dev-campusfab/chessLab/Hardware/kiCad_chessLab/cell.kicad_sch

## KiCad design Hardware/kiCad_chessLab/cell.kicad_sch (2026-09-14)

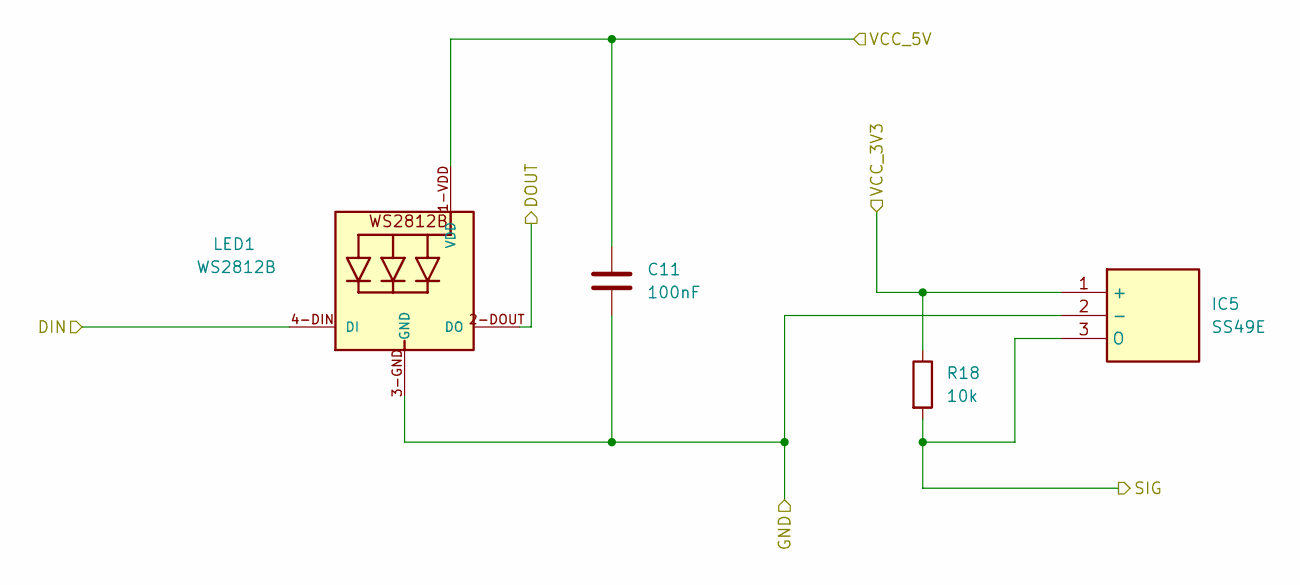
[picture p15: schematic cell.kicad_sch]

Parts:
C11: 100nF; C_0603_1608Metric_Pad1.08x0.95mm_HandSolder
IC5: SS49E; TO130P160X410X300-3P; Mouser Part Number 785-SS49E
LED1: WS2812B
R18: 10k; R_0603_1608Metric_Pad0.98x0.95mm_HandSolder

Connections:
DIN: LED1.4-DIN (DI)
DOUT: LED1.2-DOUT (DO)
GND: C11.2, IC5.2 (-), LED1.3-GND (GND)
SIG: IC5.3 (O), R18.2
VCC_3V3: IC5.1 (+), R18.1
VCC_5V: C11.1, LED1.1-VDD (VDD)
