dev-campusfab/chessLab/Hardware/kiCad_chessLab/main_board.kicad_sch

## KiCad design Hardware/kiCad_chessLab/main_board.kicad_sch (2026-09-17)

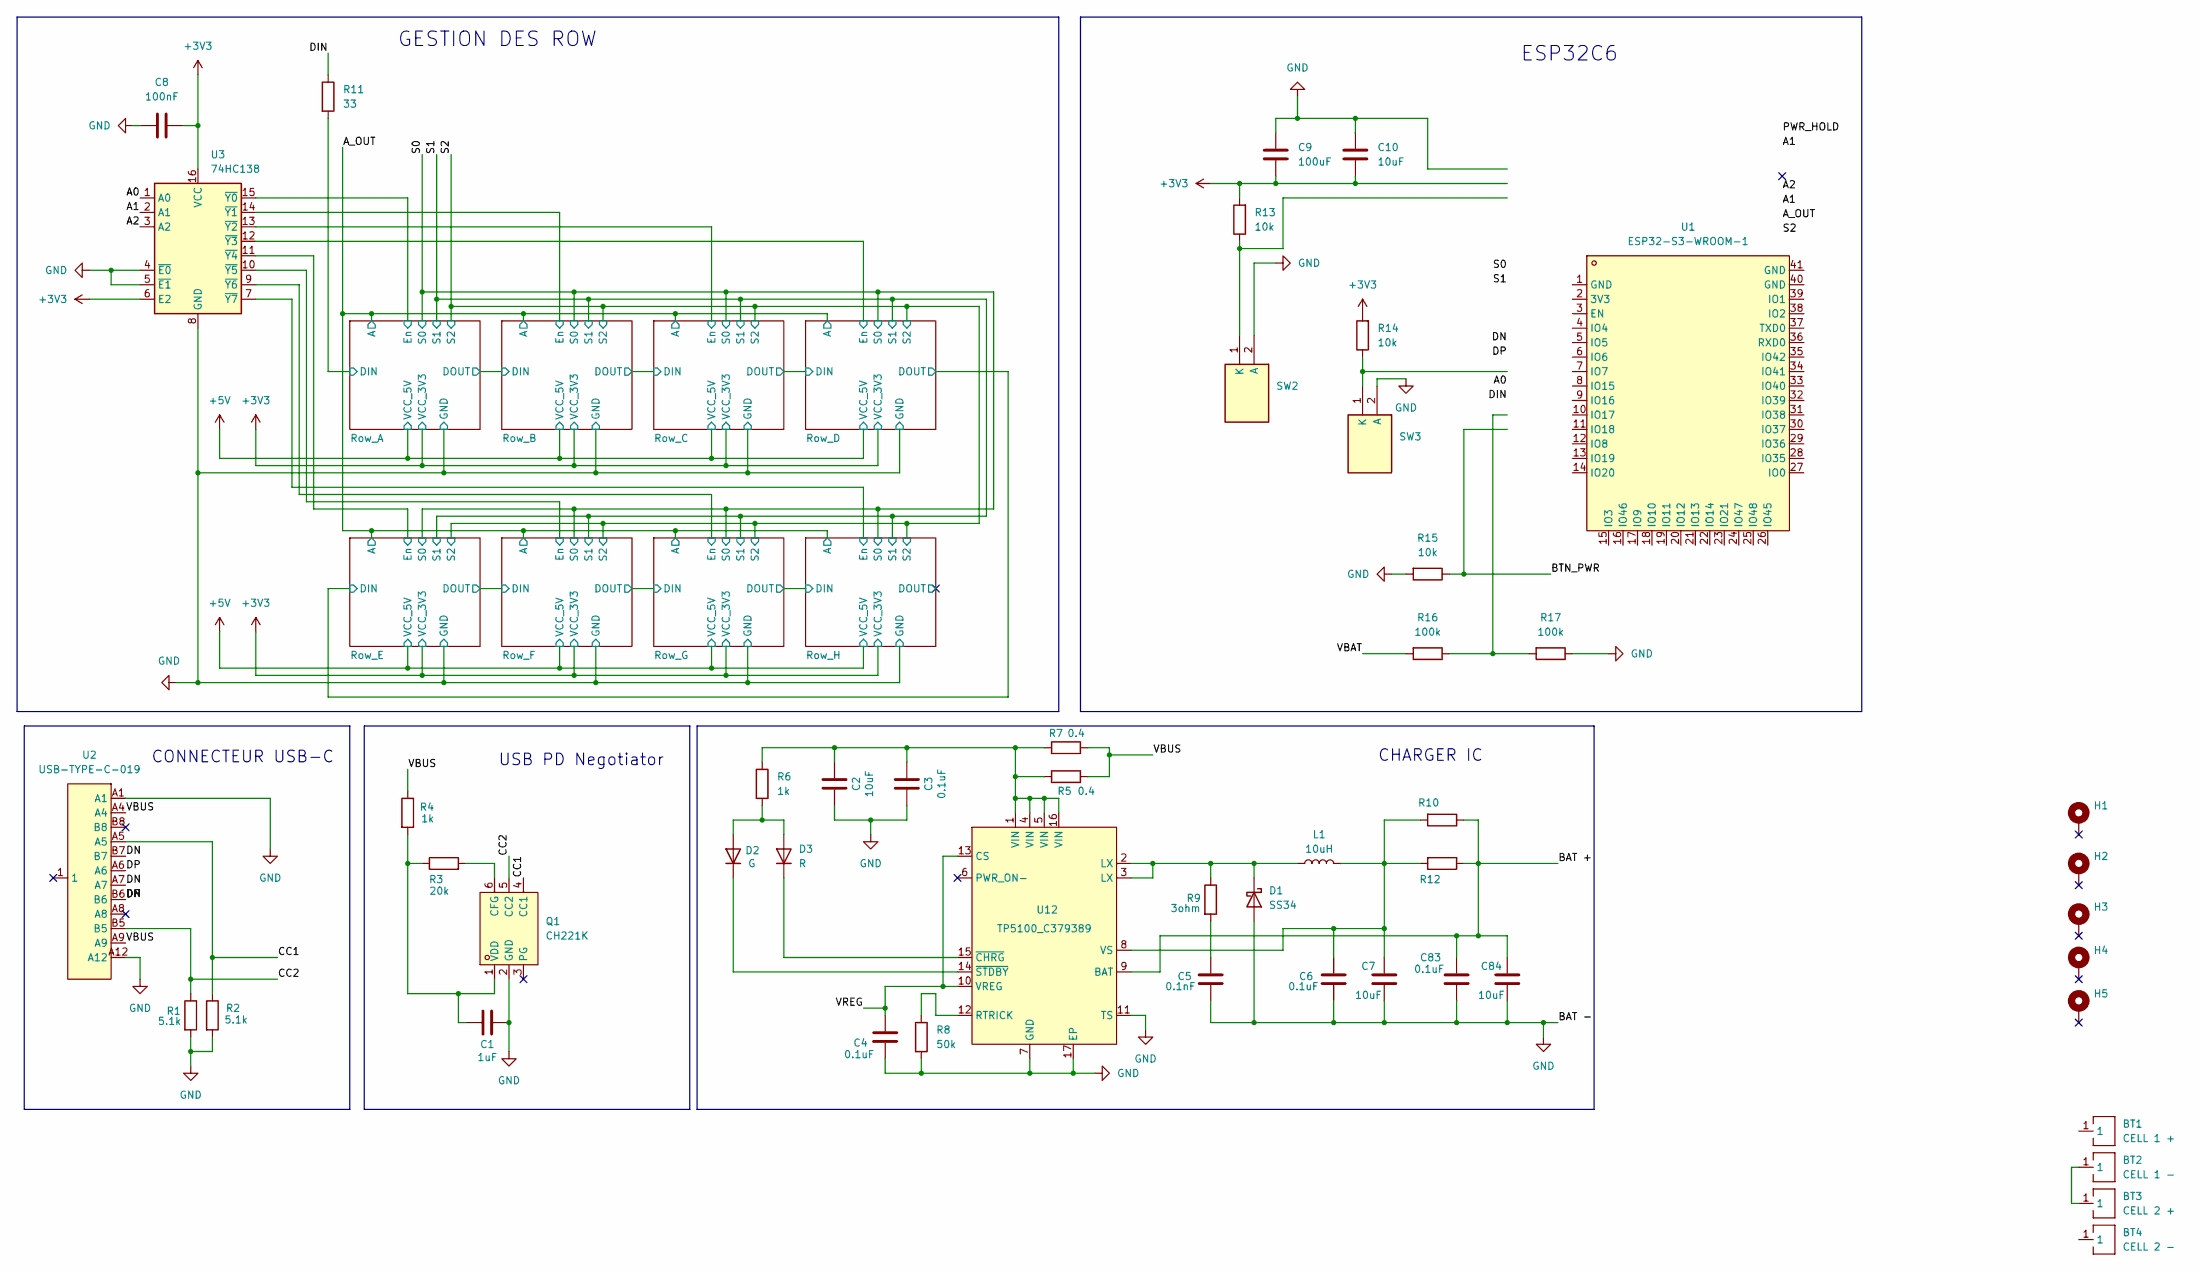
[picture p16: schematic main_board.kicad_sch]

Parts:
BT1: CELL 1 +; BAT-TH_MY-18650-01; MPN MY-18650-01; LCSC Part C2979183
BT2: CELL 1 -; BAT-TH_MY-18650-01; MPN MY-18650-01; LCSC Part C2979183
BT3: CELL 2 +; BAT-TH_MY-18650-01; MPN MY-18650-01; LCSC Part C2979183
BT4: CELL 2 -; BAT-TH_MY-18650-01; MPN MY-18650-01; LCSC Part C2979183
C1: 1uF; C_0201_0603Metric_Pad0.64x0.40mm_HandSolder
C2, C7, C84: 10uF; C_1210_3225Metric_Pad1.33x2.70mm_HandSolder
C3, C4, C6, C83: 0.1uF; C_0603_1608Metric_Pad1.08x0.95mm_HandSolder
C5: 0.1nF; C_0603_1608Metric_Pad1.08x0.95mm_HandSolder
C8: 100nF; C_0603_1608Metric_Pad1.08x0.95mm_HandSolder
C9: 100uF; C_0603_1608Metric_Pad1.08x0.95mm_HandSolder
C10: 10uF; C_0603_1608Metric_Pad1.08x0.95mm_HandSolder
D1: SS34; D_SMA_Handsoldering
D2: G; D_1206_3216Metric
D3: R; D_1206_3216Metric
H1, H2, H3, H4, H5: MountingHole_Pad; MountingHole_2.2mm_M2_DIN965_Pad
L1: 10uH; L_TechFuse_SL0520
Q1: CH221K; SOT-23-6_L2.9-W1.6-P0.95-LS2.8-BL-2; MPN CH221K; LCSC Part C5125736
R1, R2: 5.1k; R_0603_1608Metric_Pad0.98x0.95mm_HandSolder
R3: 20k; R_0603_1608Metric_Pad0.98x0.95mm_HandSolder
R4, R6: 1k; R_0603_1608Metric_Pad0.98x0.95mm_HandSolder
R5, R7: 0.4; R_1206_3216Metric_Pad1.30x1.75mm_HandSolder
R8: 50k; R_0603_1608Metric_Pad0.98x0.95mm_HandSolder
R9: 3ohm; R_0603_1608Metric_Pad0.98x0.95mm_HandSolder
R10, R12: 0,1; R_1206_3216Metric_Pad1.30x1.75mm_HandSolder
R11: 33; R_0603_1608Metric_Pad0.98x0.95mm_HandSolder
R13, R14, R15: 10k; R_0603_1608Metric_Pad0.98x0.95mm_HandSolder
R16, R17: 100k; R_0603_1608Metric_Pad0.98x0.95mm_HandSolder
SW2: RST; B3U-1000P; Mouser Part Number 653-B3U-1000P
SW3: BOOT; B3U-1000P; Mouser Part Number 653-B3U-1000P
U1: ESP32-S3-WROOM-1; WIRELM-SMD_ESP32-S3-WROOM-1; MPN ESP32-S3-WROOM-1-N16R2; LCSC Part C2913205
U2: USB-TYPE-C-019; TYPE-C-SMD_HX-TYPE-C-16PIN; MPN USB-TYPE-C-019; LCSC Part C2927039
U3: 74HC138; SOIC-16_3.9x9.9mm_P1.27mm
U12: TP5100_C379389; TQFN-16_L4.0-W4.0-P0.65-BL-EP; MPN TP5100; LCSC Part C379389

Connections:
+3V3: C8.2, C9.2, C10.2, R13.2, R14.2, U3.6 (E2), U3.16 (VCC)
A0: U3.1 (A0)
A1: U3.2 (A1)
A2: U3.3 (A2)
BAT +: C83.2, C84.2, R10.1, R12.1, U12.9 (BAT)
BTN_PWR: R15.1
CC1: Q1.4 (CC1), R2.1, U2.A5
CC2: Q1.5 (CC2), R1.1, U2.B5
DIN: R11.1, R11.2
DN: U2.A6, U2.A7, U2.B6, U2.B7
En: U3.7 (~Y7), U3.9 (~Y6), U3.10 (~Y5), U3.11 (~Y4), U3.12 (~Y3), U3.13 (~Y2), U3.14 (~Y1), U3.15 (~Y0)
GND: C1.2, C2.1, C3.1, C4.1, C5.1, C6.1, C7.1, C8.1, C9.1, C10.1, C83.1, C84.1, D1.2 (A), Q1.2 (GND), R1.2, R2.2, R8.2, R15.2, R17.1, SW2.2 (A), SW3.2 (A), U2.A1, U2.A12, U3.4 (~E0), U3.5 (~E1), U3.8 (GND), U12.7 (GND), U12.11 (TS), U12.17 (EP)
unnamed: BT2.1, BT3.1
unnamed: C1.1, Q1.1 (VDD), R3.1, R4.2
unnamed: C2.2, C3.2, R5.1, R6.1, R7.1, U12.1 (VIN), U12.4 (VIN), U12.5 (VIN), U12.16 (VIN)
unnamed: C5.2, R9.2
unnamed: C6.2, C7.2, L1.2, R10.2, R12.2, U12.8 (VS)
unnamed: D1.1 (K), L1.1, R9.1, U12.2 (LX), U12.3 (LX)
unnamed: D2.1 (K), U12.14 (~STDBY)
unnamed: D2.2 (A), D3.2 (A), R6.2
unnamed: D3.1 (K), U12.15 (~CHRG)
unnamed: Q1.6 (CFG), R3.2
unnamed: R8.1, U12.12 (RTRICK)
unnamed: R13.1, SW2.1 (K)
unnamed: R14.1, SW3.1 (K)
unnamed: R16.1, R17.2
VBAT: R16.2
VBUS: R4.1, R5.2, R7.2, U2.A4, U2.A9
VREG: C4.2, U12.10 (VREG), U12.13 (CS)

Notes on the sheet:
GESTION DES ROW
CHARGER IC
USB PD Negotiator
ESP32C6
CONNECTEUR USB-C
