dev-campusfab/chessLab/Hardware/kiCad_chessLab/power_board.kicad_sch

## KiCad design Hardware/kiCad_chessLab/power_board.kicad_sch (2026-09-14)

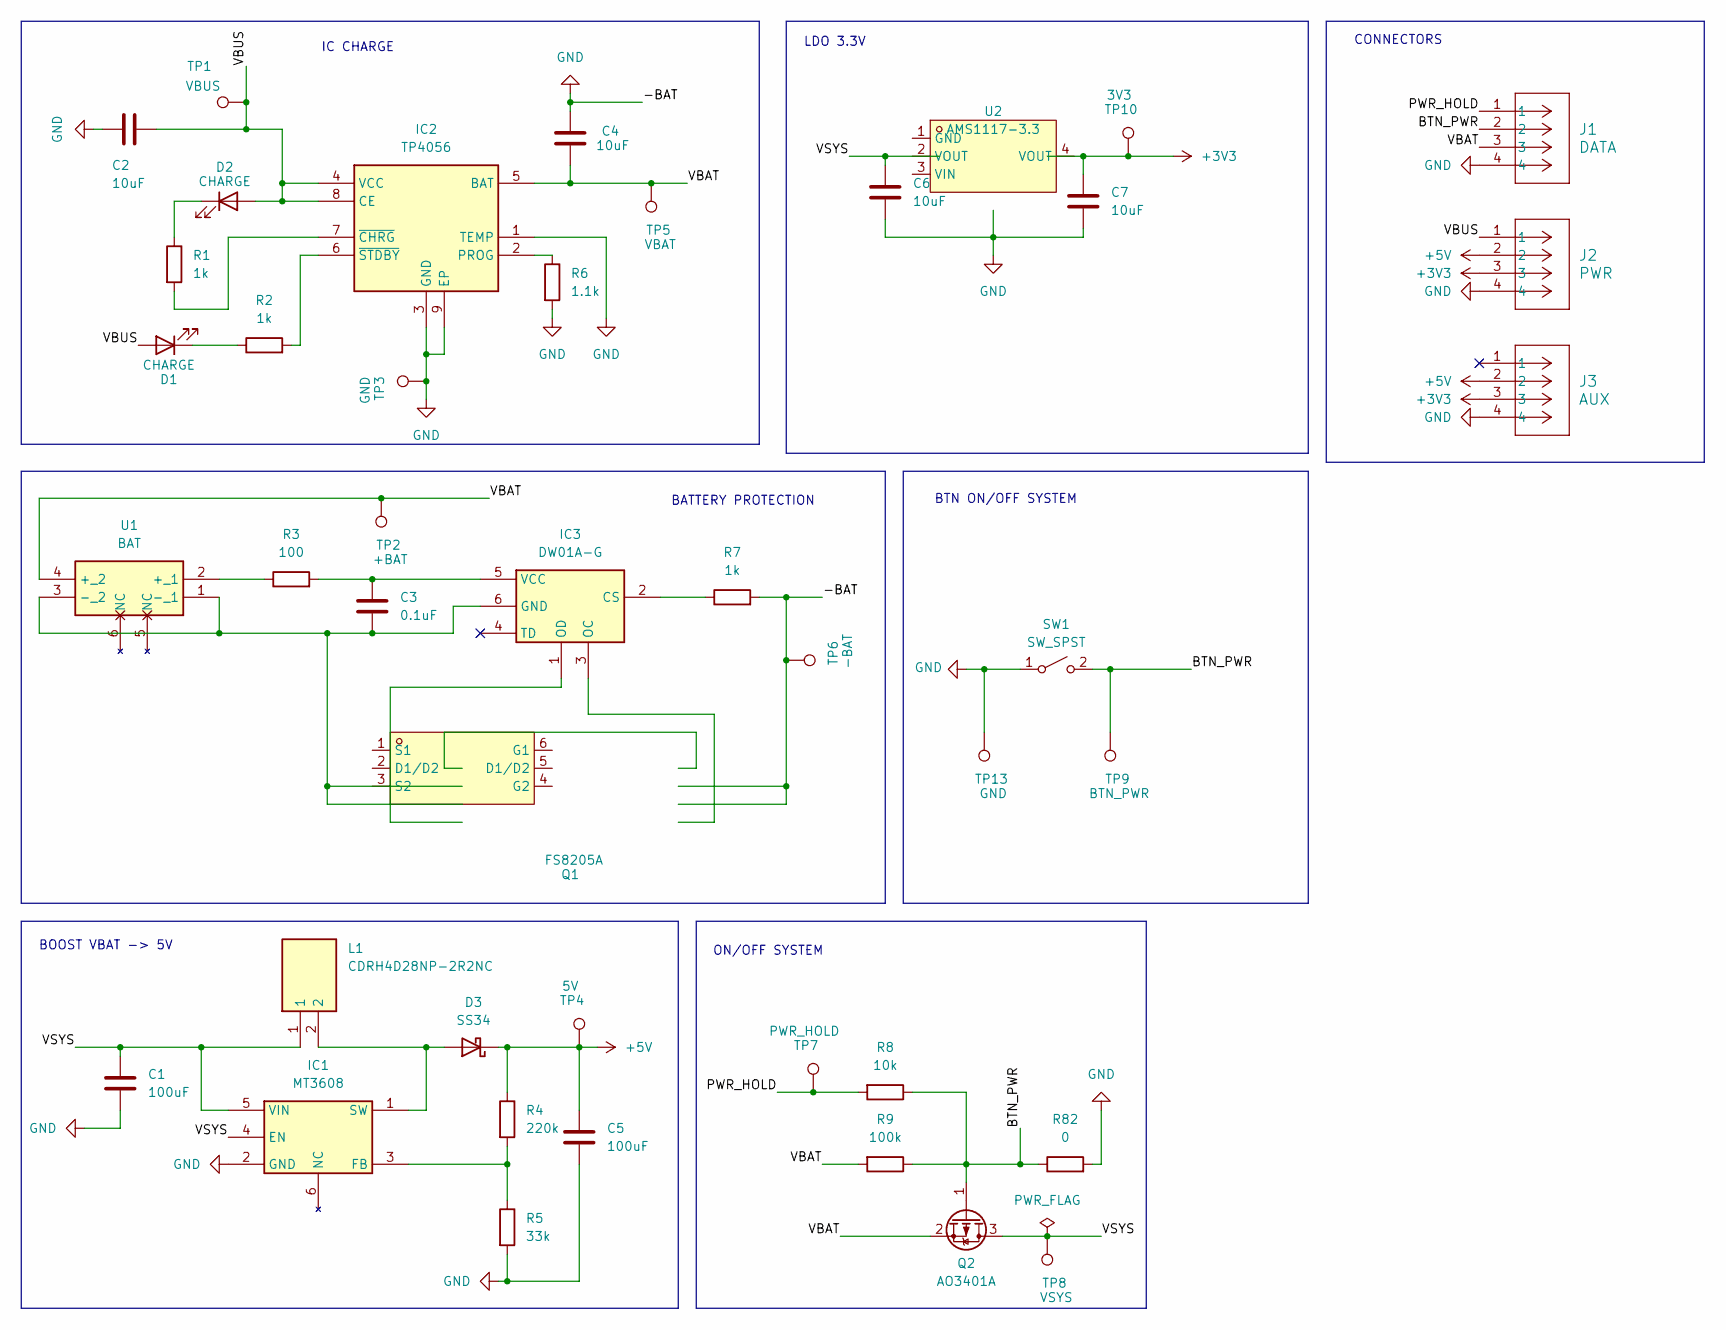
[picture p17: schematic power_board.kicad_sch]

Parts:
C1, C5: 100uF; C_1206_3216Metric_Pad1.33x1.80mm_HandSolder
C2, C4, C6, C7: 10uF; C_0603_1608Metric_Pad1.08x0.95mm_HandSolder
C3: 0.1uF; C_0603_1608Metric_Pad1.08x0.95mm_HandSolder
D1, D2: CHARGE; LED_0603_1608Metric_Pad1.05x0.95mm_HandSolder
D3: SS34; D_SMA
IC1: MT3608; SOT95P280X145-6N; Manufacturer_Part_Number MT3608
IC2: TP4056; SOIC127P600X175-9N; Manufacturer_Part_Number TP4056
IC3: DW01A-G; SOT95P280X135-6N; Manufacturer_Part_Number DW01A-G
J1: DATA; JST_XH_B4B-XH-A_1x04_P2.50mm_Vertical
J2: PWR; JST_XH_B4B-XH-A_1x04_P2.50mm_Vertical
J3: AUX; JST_XH_B4B-XH-A_1x04_P2.50mm_Vertical
L1: CDRH4D28NP-2R2NC; CDRH4D28NP100NC; Mouser Part Number 851-CDRH4D28NP-2R2NC
Q1: FS8205A; SOT-23-6_L2.9-W1.6-P0.95-LS2.8-BR; Manufacturer_Part_Number FS8205A
Q2: AO3401A; SOT-23_Handsoldering
R1, R2, R7: 1k; R_0603_1608Metric_Pad0.98x0.95mm_HandSolder
R3: 100; R_0603_1608Metric_Pad0.98x0.95mm_HandSolder
R4: 220k; R_0603_1608Metric_Pad0.98x0.95mm_HandSolder
R5: 33k; R_0603_1608Metric_Pad0.98x0.95mm_HandSolder
R6: 1.1k; R_0603_1608Metric_Pad0.98x0.95mm_HandSolder
R8: 10k; R_0603_1608Metric_Pad0.98x0.95mm_HandSolder
R9: 100k; R_0603_1608Metric_Pad0.98x0.95mm_HandSolder
R82: 0; R_0603_1608Metric_Pad0.98x0.95mm_HandSolder
SW1: SW_SPST; B3U-1000P
TP1: VBUS; TestPoint_Plated_Hole_D2.0mm
TP2: +BAT; TestPoint_Plated_Hole_D2.0mm
TP3, TP13: GND; TestPoint_Plated_Hole_D2.0mm
TP4: 5V; TestPoint_Plated_Hole_D2.0mm
TP5: VBAT; TestPoint_Plated_Hole_D2.0mm
TP6: -BAT; TestPoint_Plated_Hole_D2.0mm
TP7: PWR_HOLD; TestPoint_Plated_Hole_D2.0mm
TP8: VSYS; TestPoint_Plated_Hole_D2.0mm
TP9: BTN_PWR; TestPoint_Plated_Hole_D2.0mm
TP10: 3V3; TestPoint_Plated_Hole_D2.0mm
U1: BAT; CONN4_1048_KEY; Mouser Part Number 534-1048
U2: AMS1117-3.3; SOT-223-3_L6.5-W3.4-P2.30-LS7.0-BR

Connections:
+3V3: C7.1, J2.3, J3.3, TP10.1
+5V: C5.1, D3.1 (K), J2.2, J3.2, R4.1, TP4.1
BTN_PWR: J1.2, Q2.1 (G), R8.1, R9.1, R82.1, SW1.2 (B), TP9.1
GND: C1.2, C2.1, C4.2, C5.2, C6.2, C7.2, IC1.2 (GND), IC2.1 (TEMP), IC2.3 (GND), IC2.9 (EP), J1.4, J2.4, J3.4, R5.2, R6.2, R7.2, R82.2, SW1.1 (A), TP3.1, TP6.1, TP13.1
unnamed: C3.1, IC3.5 (VCC), R3.2
unnamed: C3.2, IC3.6 (GND), U1.1 (-_1), U1.3 (-_2)
unnamed: D1.1 (K), R2.1
unnamed: D2.1 (K), R1.1
unnamed: D3.2 (A), IC1.1 (SW), L1.2
unnamed: IC1.3 (FB), R4.2, R5.1
unnamed: IC2.2 (PROG), R6.1
unnamed: IC2.6 (~STDBY), R2.2
unnamed: IC2.7 (~CHRG), R1.2
unnamed: IC3.2 (CS), R7.1
unnamed: R3.1, U1.2 (+_1)
PWR_HOLD: J1.1, R8.2, TP7.1
VBAT: C4.1, IC2.5 (BAT), J1.3, Q2.2 (S), R9.2, TP2.1, TP5.1, U1.4 (+_2)
VBUS: C2.2, D1.2 (A), D2.2 (A), IC2.4 (VCC), IC2.8 (CE), J2.1, TP1.1
VSYS: C1.1, C6.1, IC1.4 (EN), IC1.5 (VIN), L1.1, Q2.3 (D), TP8.1

Notes on the sheet:
IC CHARGE
BTN ON/OFF SYSTEM
CONNECTORS
ON/OFF SYSTEM
BATTERY PROTECTION
BOOST VBAT -> 5V
LDO 3.3V
