dev-campusfab/chessLab/Hardware/kiCad_chessLab/row.kicad_sch

## KiCad design Hardware/kiCad_chessLab/row.kicad_sch (2026-09-14)

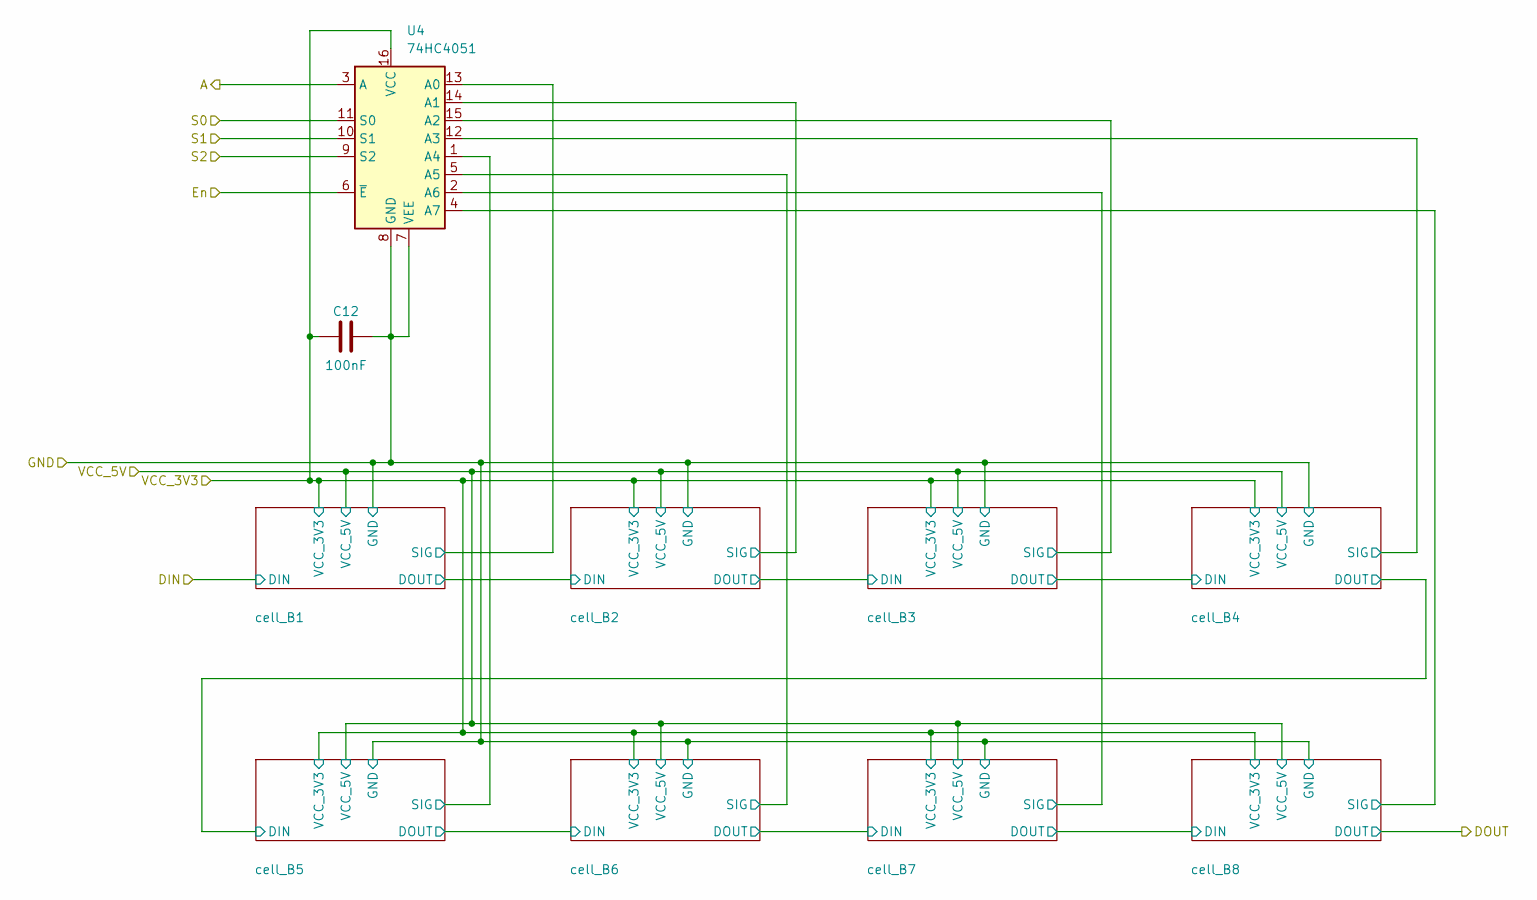
[picture p18: schematic row.kicad_sch]

Parts:
C12: 100nF; C_0603_1608Metric_Pad1.08x0.95mm_HandSolder
U4: 74HC4051; 74HC4051D653

Connections:
A: U4.3 (A)
En: U4.6 (~E)
GND: C12.2, U4.7 (VEE), U4.8 (GND)
S0: U4.11 (S0)
S1: U4.10 (S1)
S2: U4.9 (S2)
SIG: U4.1 (A4), U4.2 (A6), U4.4 (A7), U4.5 (A5), U4.12 (A3), U4.13 (A0), U4.14 (A1), U4.15 (A2)
VCC_3V3: C12.1, U4.16 (VCC)
